basbaccarne/nerdland/tests/grasshopper/cheatsheet.png

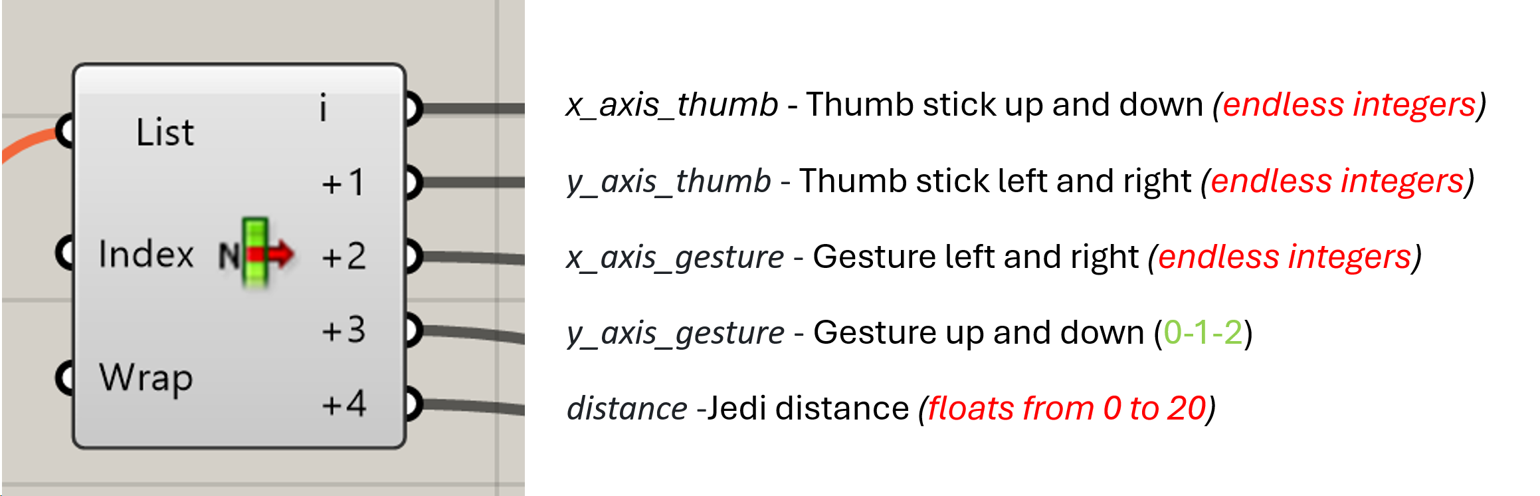
tests/grasshopper/cheatsheet.png
